ingegno/linefollower1/manual/pic/Zpart2_20140218T000856032.JPG

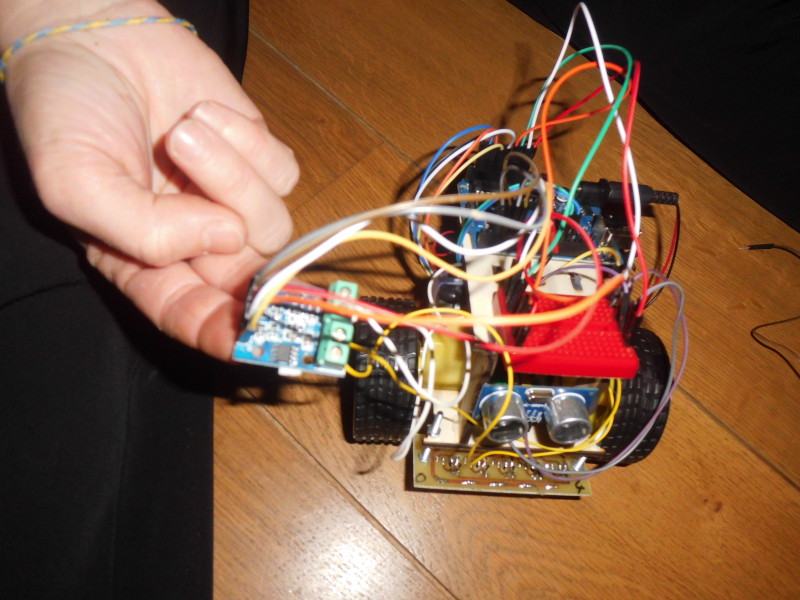
manual/pic/Zpart2_20140218T000856032.JPG
