ingegno/linefollower1/manual/pic/Zpart2_20140218T001610034.JPG

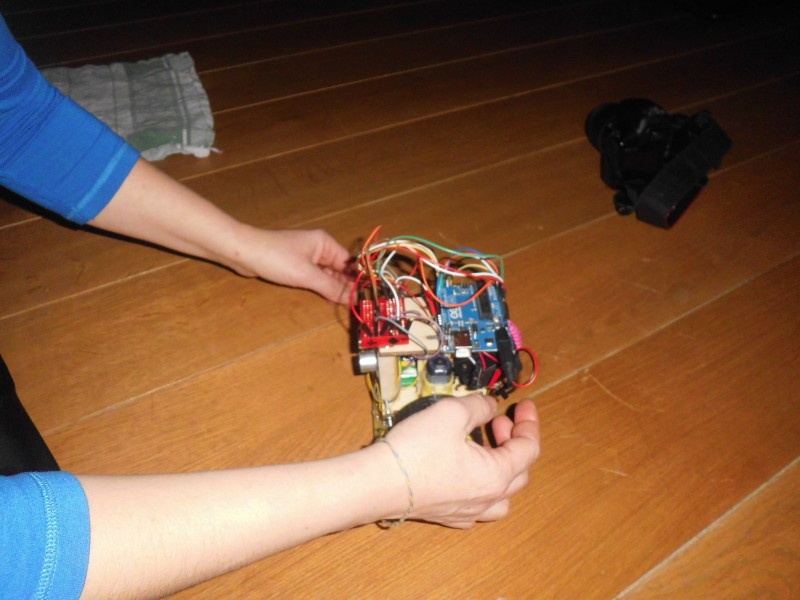
manual/pic/Zpart2_20140218T001610034.JPG
